IDMIL/T-Stick/hardware/PCB/tstick-touch-board-CraftV2/Screenshots/touch-board-schematic-view.png

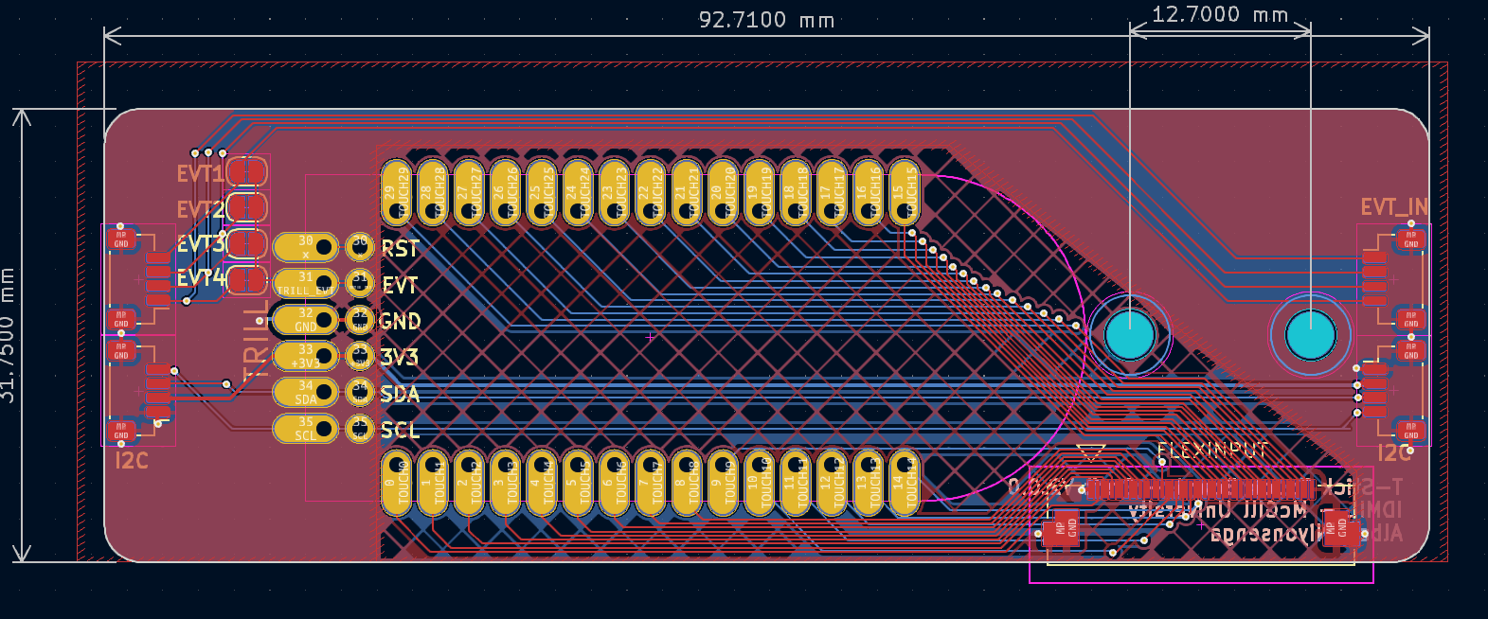
hardware/PCB/tstick-touch-board-CraftV2/Screenshots/touch-board-schematic-view.png
