IDMIL/T-Stick/hardware/PCB/tstick-touch-board-CraftV2/Screenshots/tstick-touch-board-CraftV2-back.png

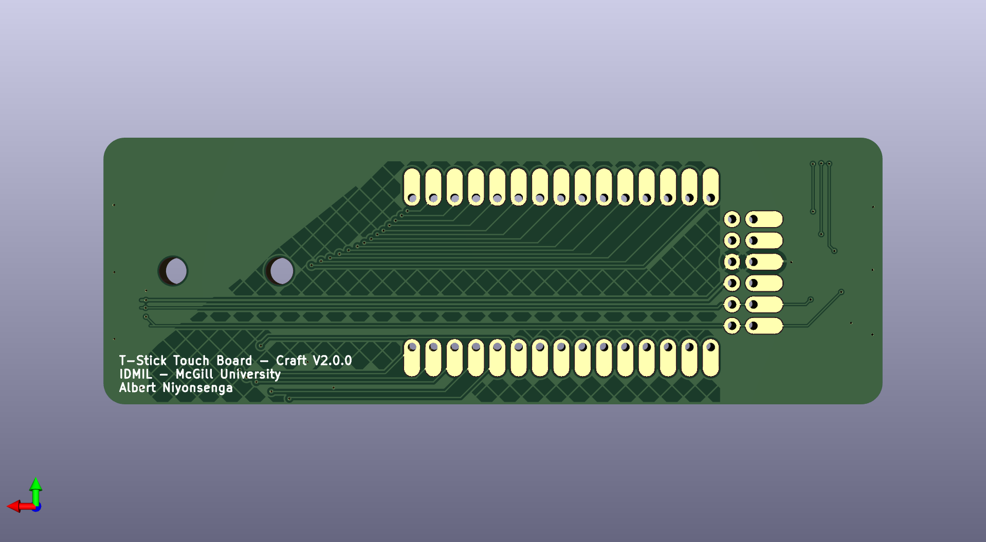
hardware/PCB/tstick-touch-board-CraftV2/Screenshots/tstick-touch-board-CraftV2-back.png
