IDMIL/T-Stick/3D_printing/T-Stick 5GW/blank-endcap.step

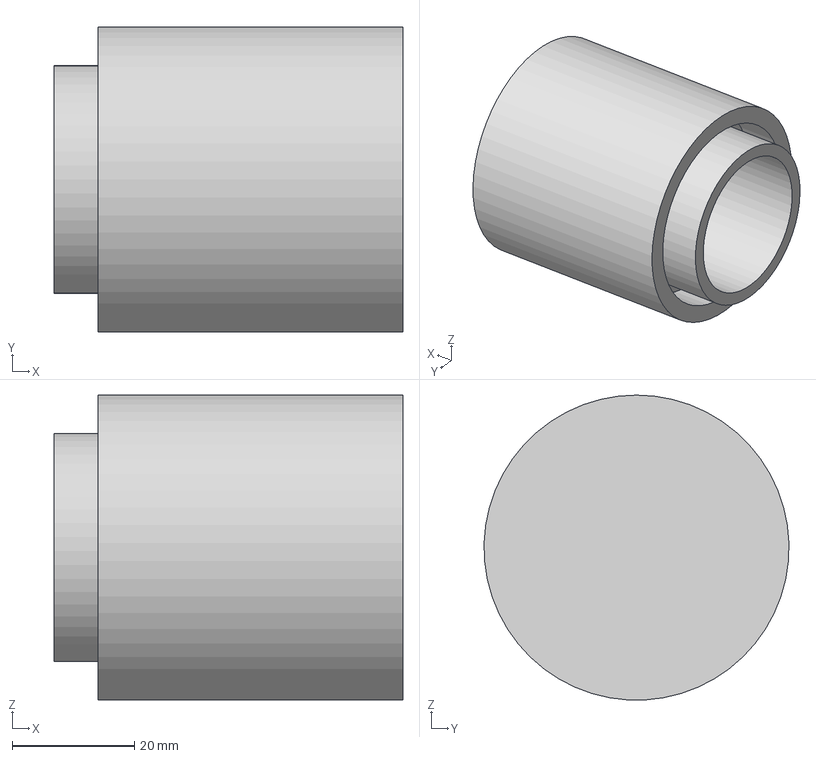
[picture p20: CAD file, 2025-09-01]
3D_printing/T-Stick 5GW/blank-endcap.step
57.2 x 50.0 x 50.0 mm
