IDMIL/T-Stick/3D_printing/T-Stick 4GW/pole.stl

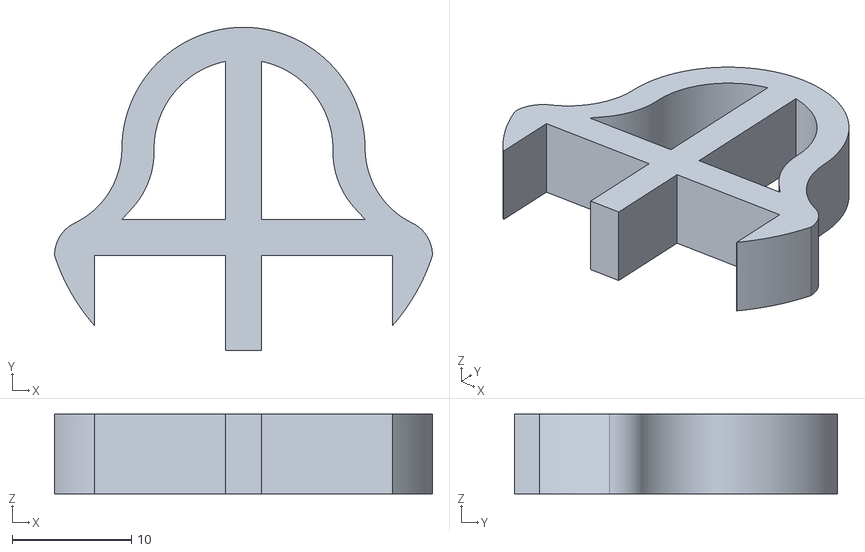
[picture p21: CAD file, 2022-04-01]
3D_printing/T-Stick 4GW/pole.stl
31.7 x 27.1 x 6.68
