IDMIL/T-Stick/3D_printing/T-Stick 4GW/pole_tinypico.stl

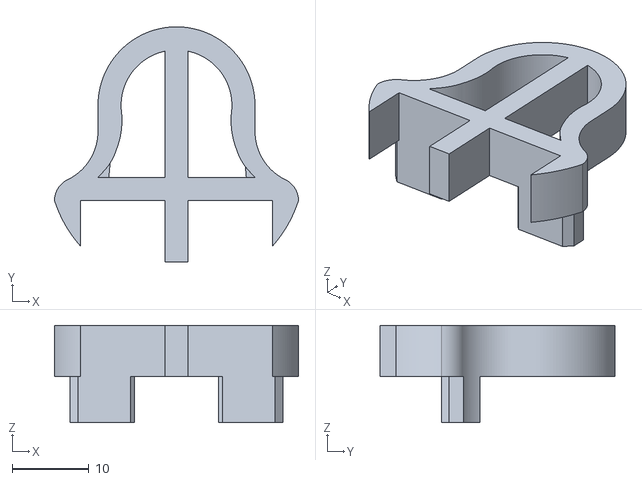
[picture p22: CAD file, 2022-04-01]
3D_printing/T-Stick 4GW/pole_tinypico.stl
31.7 x 30.6 x 12.6
