IDMIL/T-Stick/3D_printing/T-Stick 4GW/pin_scaled_0.99.stl

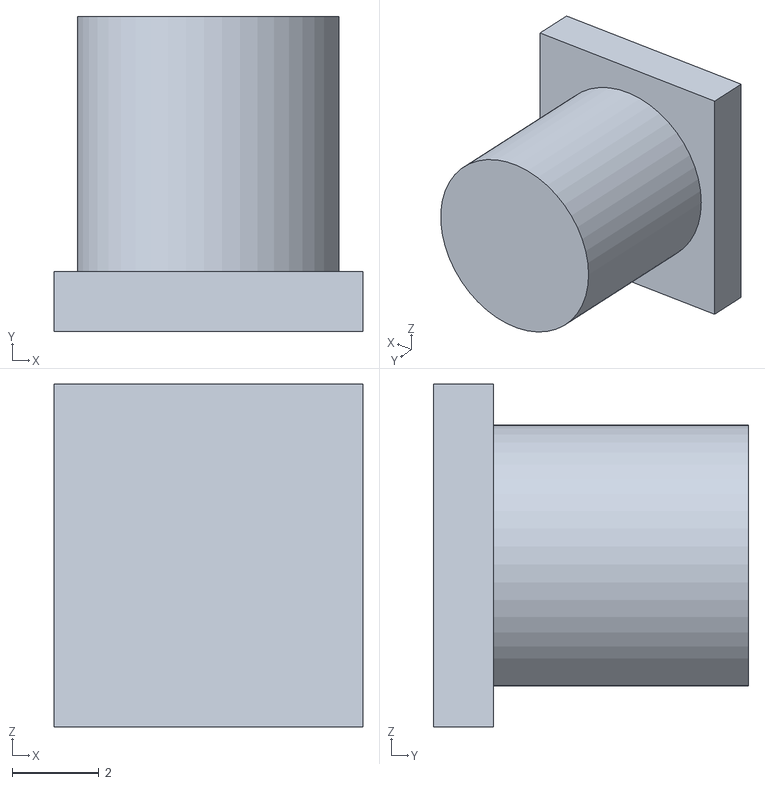
[picture p23: CAD file, 2022-04-01]
3D_printing/T-Stick 4GW/pin_scaled_0.99.stl
7.13 x 7.28 x 7.92
