IDMIL/T-Stick/Docs/images/construction/23_power.jpg

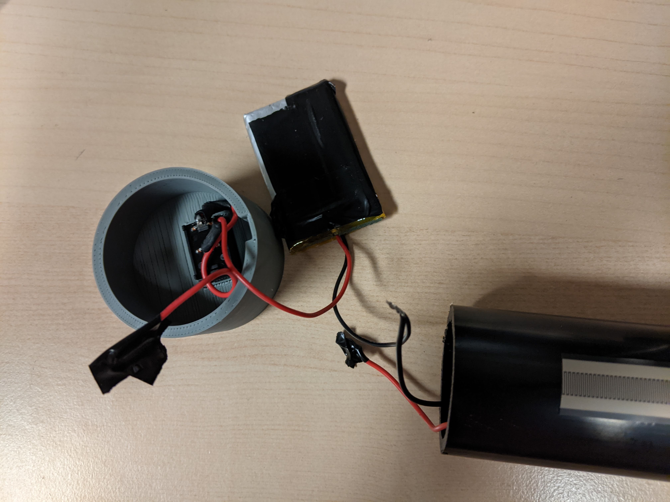
Docs/images/construction/23_power.jpg
