IDMIL/T-Stick/firmware/src/imu-cal.h

// Define IMU calibration parameters (change these parameters and recompile to apply them to T-Stick)

// Acceleration
#define ACCELZEROGX 0
#define ACCELZEROGY 0
#define ACCELZEROGZ 0

// Gyroscope
#define GYROZEROX 0
#define GYROZEROY 0
#define GYROZEROZ 0

// Magnetometer (hard offset)
#define HARDOFFSETX 0
#define HARDOFFSETY 0
#define HARDOFFSETZ 0

// Magnetometer (soft offset)
#define SOFTOFFSETX1 1
#define SOFTOFFSETX2 0
#define SOFTOFFSETX3 0

#define SOFTOFFSETY1 1
#define SOFTOFFSETY2 0
#define SOFTOFFSETY3 0

#define SOFTOFFSETZ1 1
#define SOFTOFFSETZ2 0
#define SOFTOFFSETZ3 0
